projekt-null/Gleissystem/Regelspur_Gleis/0_Einzelschwelle_Holz_K_Modul_System_v2__Hassler_Laser_Cut_Kerf_0_15.dxf

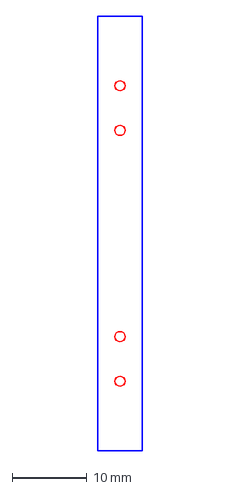
[picture p15: CAD file, 2021-12-30]
Regelspur_Gleis/0_Einzelschwelle_Holz_K_Modul_System_v2__Hassler_Laser_Cut_Kerf_0_15.dxf
5.90 x 58.2 mm
