projekt-null/Gleissystem/Regelspur_Schablonen/0_15m_Joch_Gebogen_Schablone_v8__Lenz_R10_Laser_Cut_Kerf_0_10.dxf

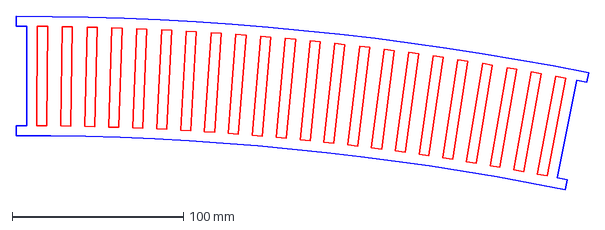
[picture p16: CAD file, 2021-12-30]
Regelspur_Schablonen/0_15m_Joch_Gebogen_Schablone_v8__Lenz_R10_Laser_Cut_Kerf_0_10.dxf
334.3 x 101.2 mm
