projekt-null/Gleissystem/Regelspur_Gleis/0_Einzelschwelle_Holz_K_Modul_System_v2__Hegob_Laser_Cut_Kerf_0_10.dxf

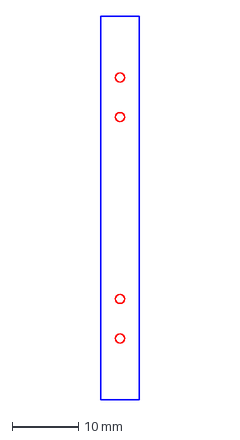
[picture p17: CAD file, 2021-12-30]
Regelspur_Gleis/0_Einzelschwelle_Holz_K_Modul_System_v2__Hegob_Laser_Cut_Kerf_0_10.dxf
5.85 x 58.1 mm
