projekt-null/Gleissystem/Regelspur_Schablonen/0_15m_Joch_Gebogen_Lenz_R10_Schablone_LaserCut_Kerf_0_15mm.dxf

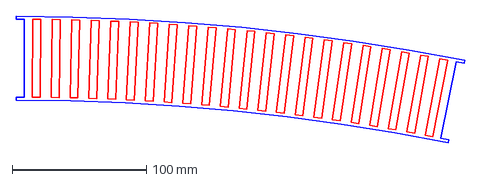
[picture p18: CAD file, 2021-12-23]
Regelspur_Schablonen/0_15m_Joch_Gebogen_Lenz_R10_Schablone_LaserCut_Kerf_0_15mm.dxf
333.7 x 94.0 mm
