projekt-null/Gleissystem/Regelspur_Schablonen/0_15m_Joch_Gebogen_2500mm_Schablone_LaserCut_Kerf_0mm.dxf

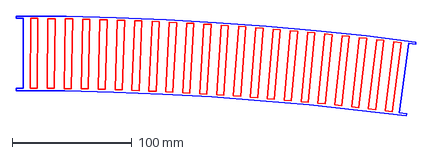
[picture p19: CAD file, 2021-12-23]
Regelspur_Schablonen/0_15m_Joch_Gebogen_2500mm_Schablone_LaserCut_Kerf_0mm.dxf
333.7 x 83.4 mm
