projekt-null/Gleissystem/Regelspur_Schablonen/0_15m_Joch_Gerade_Schablone_LaserCut_Kerf_0_10mm.dxf

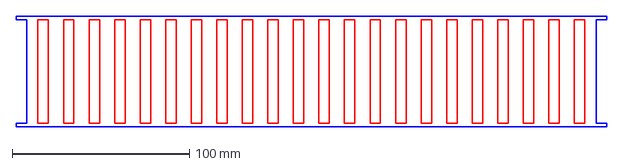
[picture p20: CAD file, 2021-12-23]
Regelspur_Schablonen/0_15m_Joch_Gerade_Schablone_LaserCut_Kerf_0_10mm.dxf
332.8 x 62.3 mm
