projekt-null/Gleissystem/Regelspur_Schablonen/0_15m_Joch_Gebogen_Lenz_R10_Schablone_LaserCut_Kerf_0_10mm.dxf

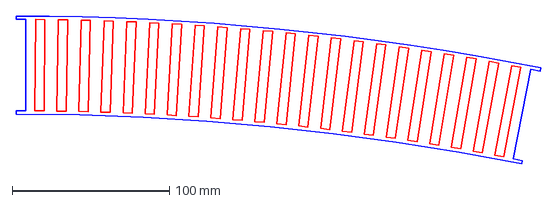
[picture p21: CAD file, 2021-12-23]
Regelspur_Schablonen/0_15m_Joch_Gebogen_Lenz_R10_Schablone_LaserCut_Kerf_0_10mm.dxf
333.6 x 93.9 mm
