projekt-null/Gleissystem/Regelspur_Schablonen/0_15m_Joch_Gebogen_2500mm_Schablone_LaserCut_Kerf_0_10mm.dxf

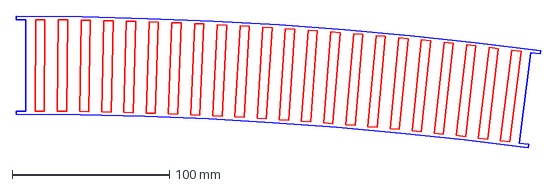
[picture p22: CAD file, 2021-12-23]
Regelspur_Schablonen/0_15m_Joch_Gebogen_2500mm_Schablone_LaserCut_Kerf_0_10mm.dxf
333.8 x 83.5 mm
