projekt-null/Gleissystem/Regelspur_Schablonen/0_15m_Joch_Gerade_Schablone_LaserCut_Kerf_0mm.dxf

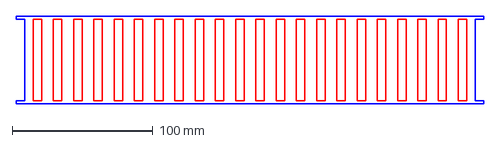
[picture p23: CAD file, 2021-12-23]
Regelspur_Schablonen/0_15m_Joch_Gerade_Schablone_LaserCut_Kerf_0mm.dxf
332.7 x 62.2 mm
